RBEGamer/SmartVolumeKnob/src/firmware/src/config.py

CFG_DEBUG: bool = True

CFG_NEOPIXEL_PIN: int = 28
CFG_NEOPIXEL_LED_COUNT: int = 12
CFG_NEOPIXEL_MAX_BRIGHTNESS: float = 1.0

CFG_ENCODER_INVERT: bool = False
CFG_ENCODER_CLK_PIN: int = 20
CFG_ENCODER_DT_PIN: int = 19
